sytsereitsma/seismometer/simulaties/analog_filter_wizard.asc

B1: bv; V=sin(0.5*time * time * 2 * pi)*0.02
C1: cap; 10µ
C2: cap; 1.6µ
C3: cap; 10µ
C4: cap; 10µ
C5: cap; 360n
C6: cap; 1.6µ; V=6.3 Irms=595m Rser=0.192493 Lser=0
R1: res; 15k
R2: res; 28.8k
R3: res; 9k
R4: res; 1k
R5: res; 161k
R6: res; 8.25k
R7: res; 9.84k
R8: res; 322k
R9: res; 1.5k
R10: res; 80.4k
U1: OP07
U2: OP07
U3: OP07
U4: OP07
V1: voltage; 15
V2: voltage; -15
Named nets: 0, 3V3, -2.5
.tran 10
.lib opamp.sub
