sytsereitsma/seismometer/simulaties/TI-artikel.asc

C1: cap; 100n
C2: cap; 1µ; V=6.3 Irms=0 Rser=0.0078 Lser=439p mfg="Würth Elektronik" pn="885012206002 WCAP-CSGP 0603" type="X7R"
C3: cap; 0.0068µ; V=16 Irms=0 Rser=0.0272 Lser=346p mfg="Würth Elektronik" pn="885012008016 WCAP-CSGP 1206" type="NP0"
C4: cap; 0.0068µ; V=16 Irms=0 Rser=0.0272 Lser=346p mfg="Würth Elektronik" pn="885012008016 WCAP-CSGP 1206" type="NP0"
C5: cap; 1µ; V=6.3 Irms=0 Rser=0.0078 Lser=439p mfg="Würth Elektronik" pn="885012206002 WCAP-CSGP 0603" type="X7R"
R1: res; 634k
R2: res; 4Meg
R3: res; 65k
R4: res; 1k
R5: res; 2Meg
R6: res; 2Meg
U1: OP07
U2: OP07
U3: OP07
V1: voltage; 15
V2: voltage; -15
V3: voltage; SINE(0 0.01 5)
Named nets: 0, 3V3, -2.5
.tran 1
.lib opamp.sub
.noise V(N004) V1 oct 100 0.01 15
